JONeillSr/FilamentTagReader/src/AWSBitmap.h

#pragma once
#include <Arduino.h>

/**
 * @file    AWSBitmap.h
 * @brief   The AwesomeWildStuff boot-logo bitmap (project-specific data).
 *
 * Kept separate from the generic SplashScreen library so the animator stays
 * logo-agnostic. Pass these to SplashScreen:
 *   SplashScreen splash(display, AWS_LOGO, AWS_LOGO_W, AWS_LOGO_H, AWS_LOGO_REST_Y);
 *
 * The bitmap is 1-bit, Adafruit_GFX drawBitmap format.
 */

static const uint16_t AWS_LOGO_W = 128;
static const uint16_t AWS_LOGO_H = 50;
// Rest near the top so it sits in the blue zone of a 2-color OLED (matches the
// original splash placement). Use -1 with SplashScreen for vertical centering.
// use 17 for placement in only the blue section of the screen
static const int16_t  AWS_LOGO_REST_Y = -1;

// 'AwesomeWildStuff', 128x50px
const unsigned char AWS_LOGO [] PROGMEM = {
	0x00, 0x78, 0x1e, 0x07, 0x03, 0xc7, 0xff, 0x81, 0xf0, 0x00, 0xf8, 0x03, 0x80, 0x07, 0x1f, 0xff,
	0x00, 0xfc, 0x1e, 0x0f, 0x83, 0xcf, 0xff, 0x87, 0xfe, 0x07, 0xff, 0x03, 0xc0, 0x0f, 0x1f, 0xff,
	0x01, 0xfc, 0x1e, 0x0f, 0x87, 0xcf, 0xff, 0x8f, 0xfe, 0x0f, 0xff, 0x83, 0xe0, 0x1f, 0x1f, 0xff,
	0x01, 0xfc, 0x1f, 0x1f, 0x87, 0x8f, 0xff, 0x9f, 0xfc, 0x1f, 0xff, 0xc3, 0xe0, 0x3f, 0x1f, 0xff,
	0x03, 0xfc, 0x1f, 0x1f, 0x8f, 0x8f, 0x80, 0x1f, 0x18, 0x3f, 0x0f, 0xc3, 0xf0, 0x7f, 0x1e, 0x00,
	0x03, 0xfe, 0x0f, 0x1f, 0x8f, 0x0f, 0x00, 0x1f, 0x00, 0x7e, 0x07, 0xe7, 0xf0, 0x7f, 0x1e, 0x00,
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
	0x00, 0x00, 0x00, 0x00, 0x00, 0x00, 0x00, 0x00, 0x00, 0x00, 0x00, 0x00, 0x00, 0x00, 0x00, 0x00,
	0x00, 0x00, 0x00, 0x00, 0x03, 0xe7, 0xfe, 0xf1, 0xe7, 0xf9, 0xfe, 0x00, 0x00, 0x00, 0x00, 0x00,
	0x00, 0x00, 0x00, 0x00, 0x0f, 0xf7, 0xfe, 0xe1, 0xcf, 0xf9, 0xfe, 0x00, 0x00, 0x00, 0x00, 0x00,
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
};
